NordicPlayground/nrf5-eagle-reference-design/nRF51x22_reference/nRF51x22_qfaa/nRF51x22_qfaa.brd

## EAGLE design nRF51x22_reference/nRF51x22_qfaa/nRF51x22_qfaa.brd (2016-06-28)

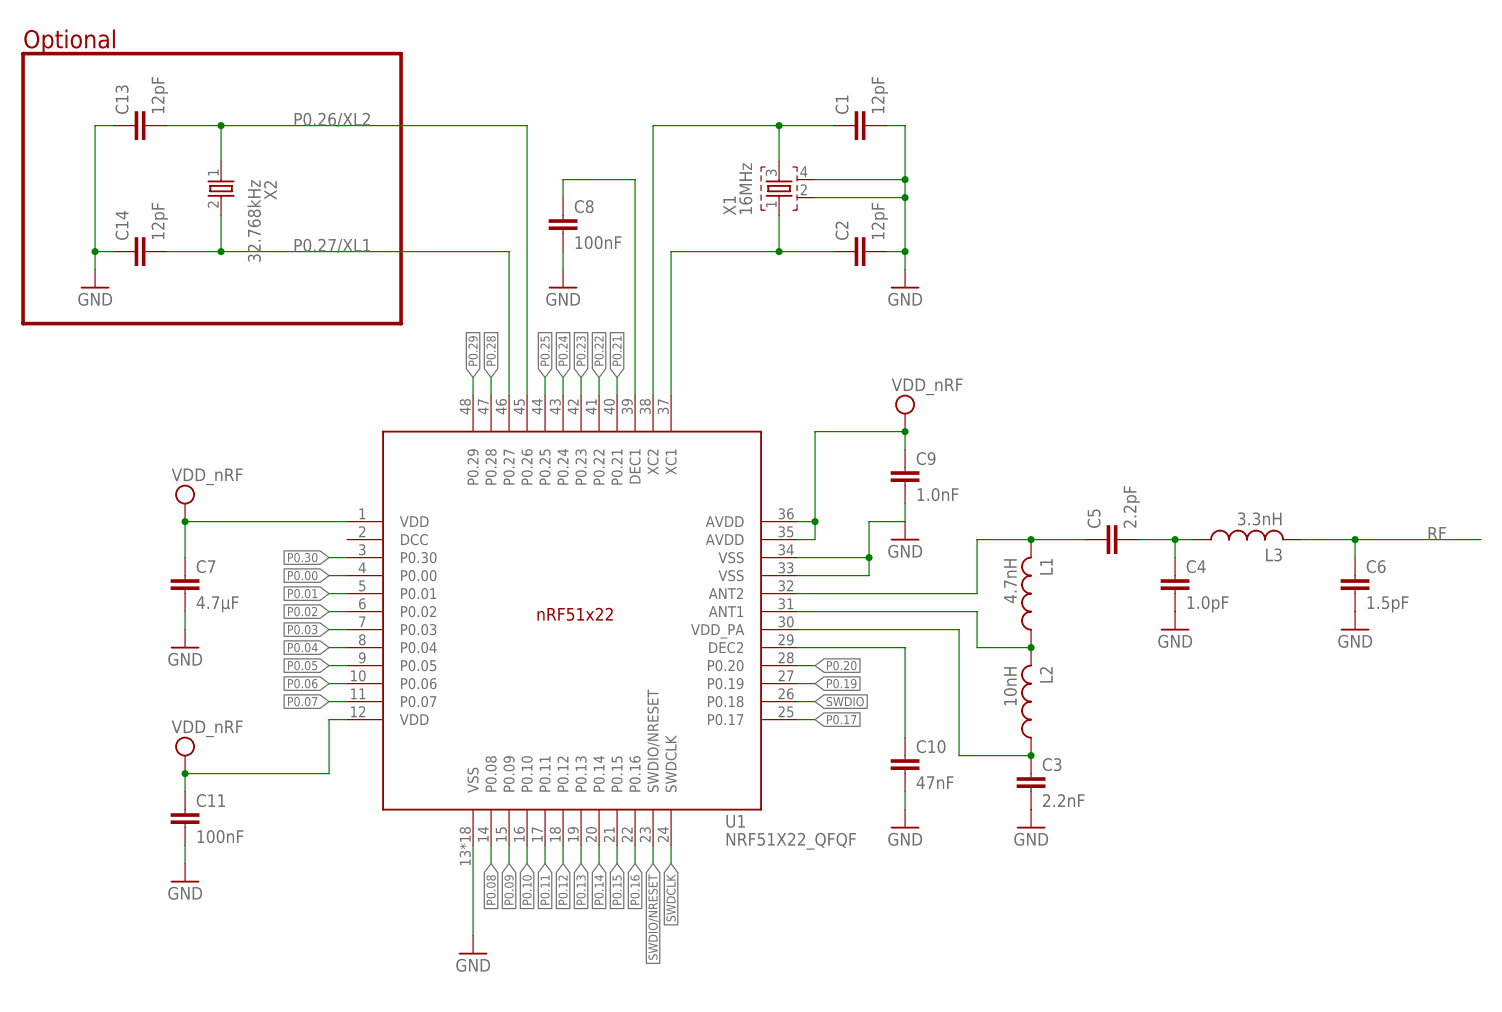
[picture p10: schematic nRF51x22_qfaa.sch]

Parts:
C1, C2, C13, C14: 12pF; RESC0402_N
C3: 2.2nF; RESC0402_N
C4: 1.0pF; RESC0402_N
C5: 2.2pF; RESC0402_N
C6: 1.5pF; RESC0402_N
C7: 4.7µF; RESC0603_N
C8, C11: 100nF; RESC0402_N
C9: 1.0nF; RESC0402_N
C10: 47nF; RESC0402_N
L1: 4.7nH; RESC0402_N
L2: 10nH; RESC0402_N
L3: 3.3nH; RESC0402_N
U1: NRF51X22_QFQF; QFN40P600X600X90-48_N
X1: 16MHz; BT-XTAL_2016_N
X2: 32.768kHz; XTAL_3215_N

Connections:
DCC: U1.2 (DCC)
GND: C1.2, C2.2, C3.2, C4.2, C6.2, C7.2, C8.2, C9.2, C10.2, C11.2, C13.1, C14.1, U1.13 (VSS), U1.33 (VSS), U1.34 (VSS), U1.PAD (VSS), U1.PAD@VIA01 (VSS), U1.PAD@VIA02 (VSS), U1.PAD@VIA03 (VSS), U1.PAD@VIA04 (VSS), U1.PAD@VIA05 (VSS), U1.PAD@VIA06 (VSS), U1.PAD@VIA07 (VSS), U1.PAD@VIA08 (VSS), U1.PAD@VIA09 (VSS), U1.PAD@VIA10 (VSS), U1.PAD@VIA11 (VSS), U1.PAD@VIA12 (VSS), U1.PAD@VIA13 (VSS), U1.PAD@VIA14 (VSS), U1.PAD@VIA15 (VSS), U1.PAD@VIA16 (VSS), X1.2, X1.4
unnamed: L1.1, L2.2, U1.31 (ANT1)
unnamed: C1.1, U1.38 (XC2), X1.3
unnamed: C10.1, U1.29 (DEC2)
unnamed: C8.1, U1.39 (DEC1)
unnamed: C3.1, L2.1, U1.30 (VDD_PA)
unnamed: C5.1, L1.2, U1.32 (ANT2)
unnamed: C4.1, C5.2, L3.1
P0.00: U1.4 (P0.00)
P0.01: U1.5 (P0.01)
P0.02: U1.6 (P0.02)
P0.03: U1.7 (P0.03)
P0.04: U1.8 (P0.04)
P0.05: U1.9 (P0.05)
P0.06: U1.10 (P0.06)
P0.07: U1.11 (P0.07)
P0.08: U1.14 (P0.08)
P0.09: U1.15 (P0.09)
P0.10: U1.16 (P0.10)
P0.11: U1.17 (P0.11)
P0.12: U1.18 (P0.12)
P0.13: U1.19 (P0.13)
P0.14: U1.20 (P0.14)
P0.15: U1.21 (P0.15)
P0.16: U1.22 (P0.16)
P0.17: U1.25 (P0.17)
P0.19: U1.27 (P0.19)
P0.20: U1.28 (P0.20)
P0.21: U1.40 (P0.21)
P0.22: U1.41 (P0.22)
P0.23: U1.42 (P0.23)
P0.24: U1.43 (P0.24)
P0.25: U1.44 (P0.25)
P0.26/XL2: C13.2, U1.45 (P0.26), X2.1
P0.27/XL1: C14.2, U1.46 (P0.27), X2.2
P0.28: U1.47 (P0.28)
P0.29: U1.48 (P0.29)
P0.30: U1.3 (P0.30)
RF: C6.1, L3.2
SWDCLK: U1.24 (SWDCLK)
SWDIO: U1.26 (P0.18)
SWDIO/NRESET: U1.23 (SWDIO/NRESET)
VDD_NRF: C7.1, C9.1, C11.1, U1.1 (VDD), U1.12 (VDD), U1.35 (AVDD), U1.36 (AVDD)
X1: C2.1, U1.37 (XC1), X1.1

Notes on the sheet:
Optional

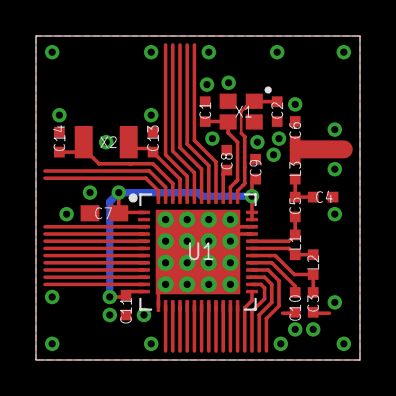
[picture p11: board nRF51x22_qfaa.brd from above]

Board: 2 copper layers, 18.0 x 18.0 mm, 19 parts (0 on the bottom side), 13 nets.
