NordicPlayground/nrf5-eagle-reference-design/nRF52832_MCU_Board/nRF52832_MCU_nano/nRF52832_MCU.brd

## EAGLE design nRF52832_MCU_Board/nRF52832_MCU_nano/nRF52832_MCU.brd (2016-06-23)

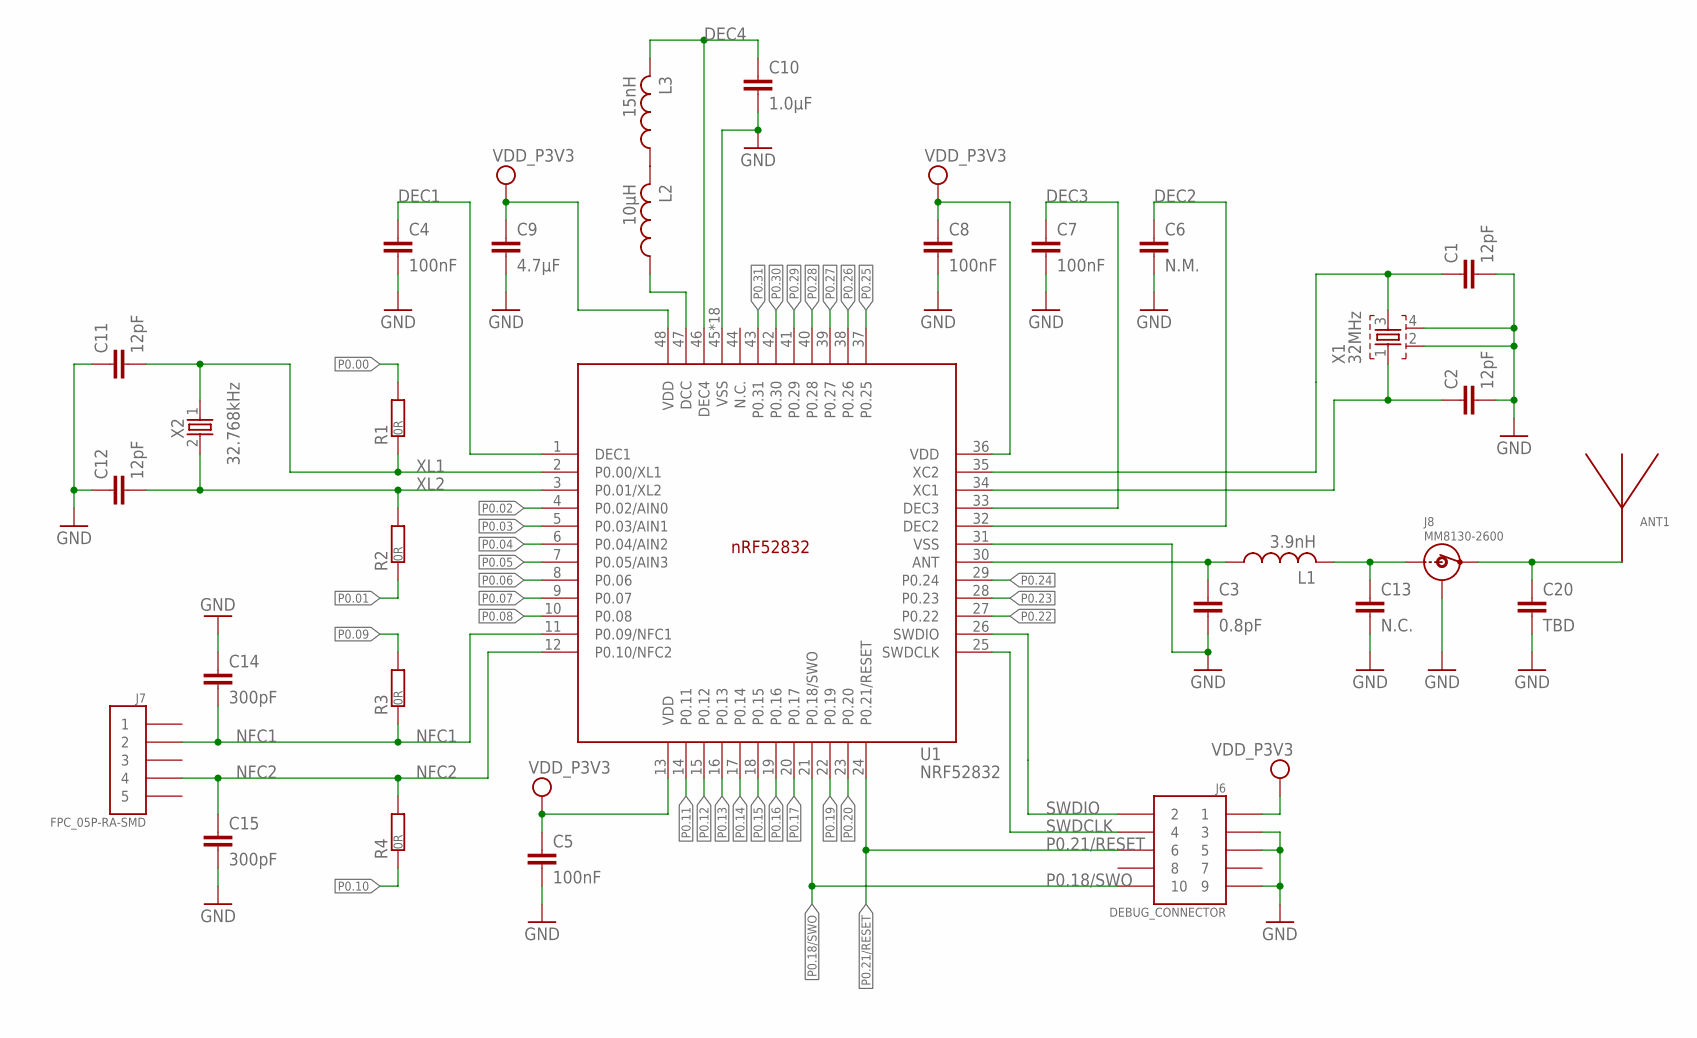
[picture p12: schematic nRF52832_MCU.sch, sheet 1]

Parts:
ANT1: ANTENNA_QUARTER-WAVE_MONOPOLE_MEANDERED_LEFT; QWMP_MEANDERED_LEFT_+6
C1, C2, C11, C12: 12pF; RESC0402_N
C3: 0.8pF; RESC0402_N
C4, C5, C7, C8: 100nF; RESC0402_N
C6: N.M.; RESC0402_N
C9: 4.7µF; RESC0603_N
C10: 1.0µF; RESC0603_N
C13: N.C.; RESC0402_N
C14, C15: 300pF; RESC0402_N
C20: TBD; RESC0402_N
J6: DEBUG_CONNECTOR; HDRV127P5X2-10_N
J7: FPC_05P-RA-SMD
J8: MM8130-2600
L1: 3.9nH; RESC0402_N
L2: 10µH; RESC0603_N
L3: 15nH; RESC0402_N
R1, R2, R3, R4: 0R; RESC0402_N
U1: NRF52832; QFN40P600X600X90-48_N
X1: 32MHz; BT-XTAL_2016_N
X2: 32.768kHz; XTAL_3215_N

Connections:
ANT: C3.1, L1.1, U1.30 (ANT)
DEC1: C4.1, U1.1 (DEC1)
DEC2: C6.1, U1.32 (DEC2)
DEC3: C7.1, U1.33 (DEC3)
DEC4: C10.1, L3.2, U1.46 (DEC4)
GND: C1.2, C2.2, C3.2, C4.2, C5.2, C6.2, C7.2, C8.2, C9.2, C10.2, C11.1, C12.1, C13.2, C14.1, C15.2, C20.2, J6.3, J6.5, J6.9, J8.1, J8.2, J8.3, J8.4, U1.31 (VSS), U1.45 (VSS), U1.PAD (VSS), U1.PAD@VIA01 (VSS), U1.PAD@VIA02 (VSS), U1.PAD@VIA03 (VSS), U1.PAD@VIA04 (VSS), U1.PAD@VIA05 (VSS), U1.PAD@VIA06 (VSS), U1.PAD@VIA07 (VSS), U1.PAD@VIA08 (VSS), U1.PAD@VIA09 (VSS), U1.PAD@VIA10 (VSS), U1.PAD@VIA11 (VSS), U1.PAD@VIA12 (VSS), U1.PAD@VIA13 (VSS), U1.PAD@VIA14 (VSS), U1.PAD@VIA15 (VSS), U1.PAD@VIA16 (VSS), X1.2, X1.4; also elsewhere on the board
unnamed: ANT1.P$1, C20.1, J8.OUT
unnamed: L2.2, L3.1
unnamed: C1.1, U1.35 (XC2), X1.3
unnamed: L2.1, U1.47 (DCC)
unnamed: C13.1, J8.IN, L1.2
NFC1: C14.2, J7.2, R3.1, U1.11 (P0.09/NFC1)
NFC2: C15.1, J7.4, R4.2, U1.12 (P0.10/NFC2)
P0.00: R1.2; also elsewhere on the board
P0.01: R2.1; also elsewhere on the board
P0.02: U1.4 (P0.02/AIN0); also elsewhere on the board
P0.03: U1.5 (P0.03/AIN1); also elsewhere on the board
P0.04: U1.6 (P0.04/AIN2); also elsewhere on the board
P0.05: U1.7 (P0.05/AIN3); also elsewhere on the board
P0.06: U1.8 (P0.06); also elsewhere on the board
P0.07: U1.9 (P0.07); also elsewhere on the board
P0.08: U1.10 (P0.08); also elsewhere on the board
P0.09: R3.2; also elsewhere on the board
P0.10: R4.1; also elsewhere on the board
P0.11: U1.14 (P0.11); also elsewhere on the board
P0.12: U1.15 (P0.12); also elsewhere on the board
P0.13: U1.16 (P0.13); also elsewhere on the board
P0.14: U1.17 (P0.14); also elsewhere on the board
P0.15: U1.18 (P0.15); also elsewhere on the board
P0.16: U1.19 (P0.16); also elsewhere on the board
P0.17: U1.20 (P0.17); also elsewhere on the board
P0.18/SWO: J6.10, U1.21 (P0.18/SWO); also elsewhere on the board
P0.19: U1.22 (P0.19); also elsewhere on the board
P0.20: U1.23 (P0.20); also elsewhere on the board
P0.21/RESET: J6.6, U1.24 (P0.21/RESET); also elsewhere on the board
P0.22: U1.27 (P0.22); also elsewhere on the board
P0.23: U1.28 (P0.23); also elsewhere on the board
P0.24: U1.29 (P0.24); also elsewhere on the board
P0.25: U1.37 (P0.25); also elsewhere on the board
P0.26: U1.38 (P0.26); also elsewhere on the board
P0.27: U1.39 (P0.27); also elsewhere on the board
P0.28: U1.40 (P0.28); also elsewhere on the board
P0.29: U1.41 (P0.29); also elsewhere on the board
P0.30: U1.42 (P0.30); also elsewhere on the board
P0.31: U1.43 (P0.31); also elsewhere on the board
SWDCLK: J6.4, U1.25 (SWDCLK)
SWDIO: J6.2, U1.26 (SWDIO)
VDD_P3V3: C5.1, C8.1, C9.1, J6.1, U1.13 (VDD), U1.36 (VDD), U1.48 (VDD); also elsewhere on the board
X1: C2.1, U1.34 (XC1), X1.1
XL1: C11.2, R1.1, U1.2 (P0.00/XL1), X2.1
XL2: C12.2, R2.2, U1.3 (P0.01/XL2), X2.2

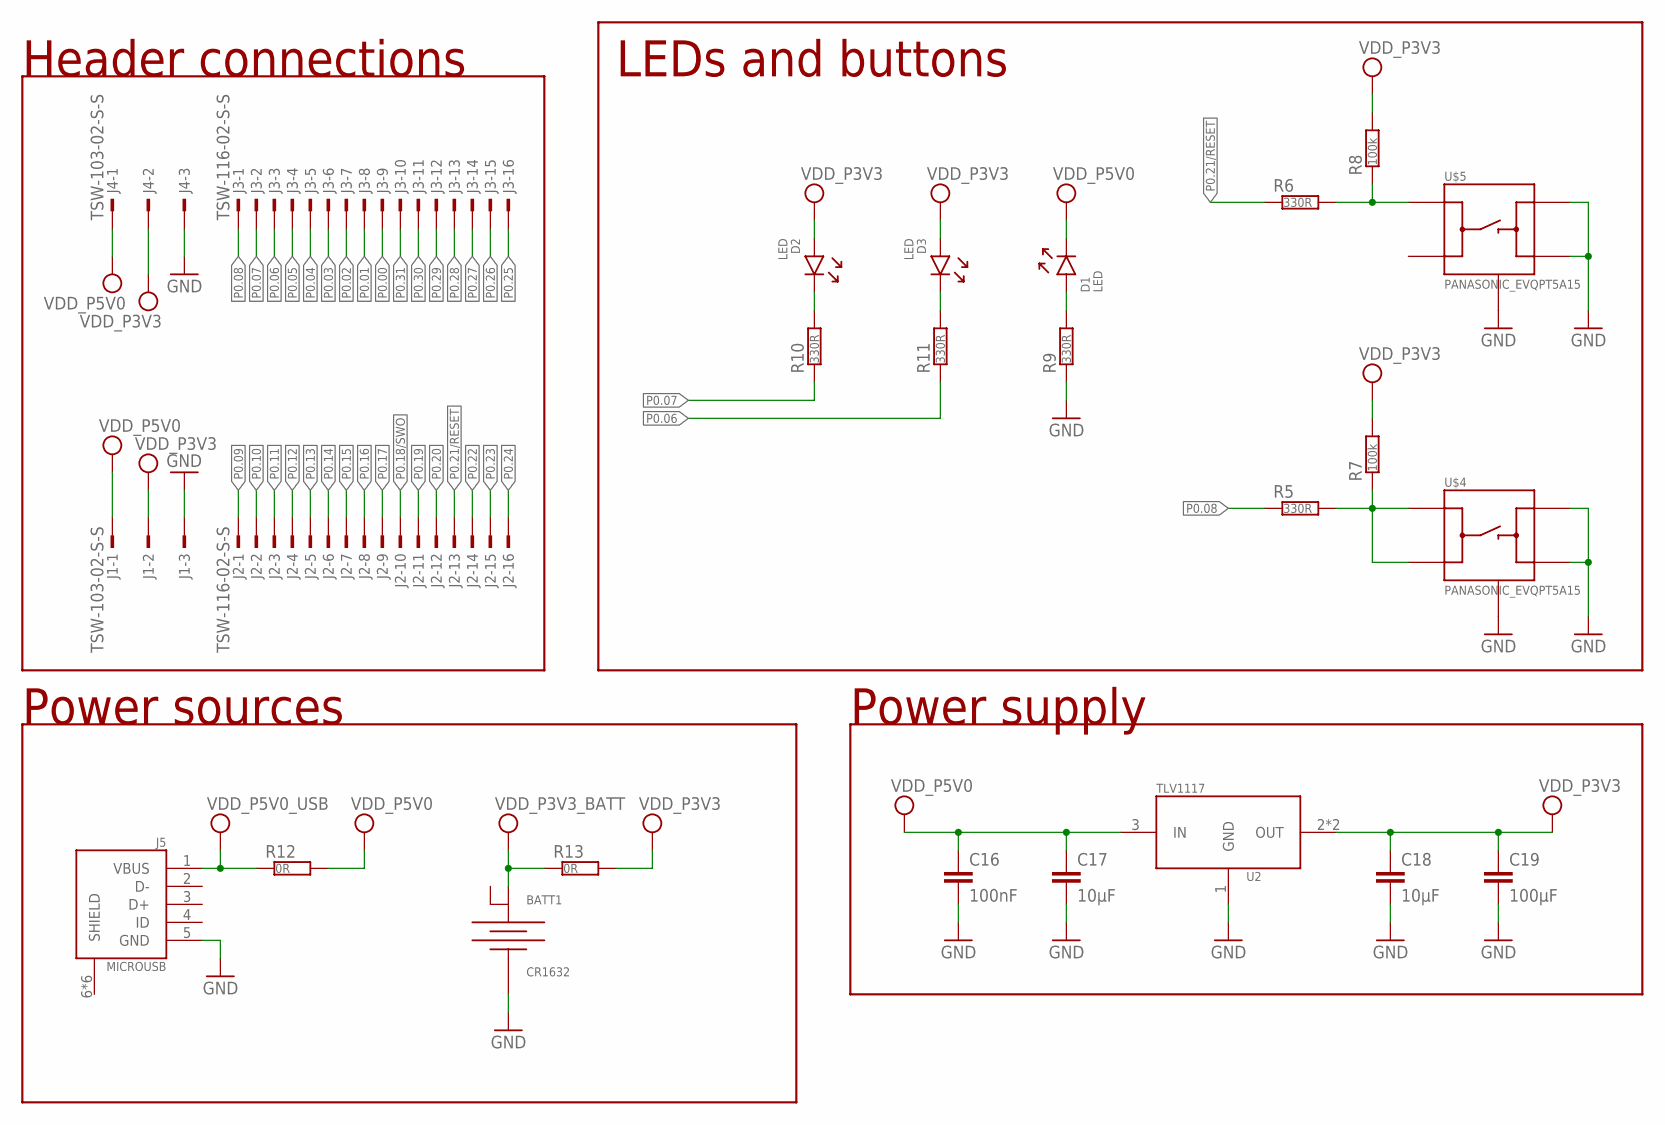
[picture p13: schematic nRF52832_MCU.sch, sheet 2]

Parts:
BATT1: CR1632; CR1632_HOLDER_TH
C16: 100nF; RESC0402_N
C17, C18: 10µF; RESC0603_N
C19: 100µF; RESC0805_N
D1, D2, D3: LED; DIOC0603_N
J1, J4: TSW-103-02-S-S
J2, J3: TSW-116-02-S-S
J5: MICROUSB; USB-MICRO-B-RA-SMD-PIP
R5, R6, R9, R10, R11: 330R; RESC0402_N
R7, R8: 100k; RESC0402_N
R12, R13: 0R; RESC0402_N
U2: TLV1117; SOT220P700-4_N
U$4, U$5: PANASONIC_EVQPT5A15

Connections:
GND: BATT1.1 (-), C16.2, C17.2, C18.2, C19.2, J1.3, J4.3, J5.5 (GND), R9.1, U2.1 (GND), U$4.3 (B), U$4.4 (B'), U$4.5 (GND), U$4.6 (GND), U$5.3 (B), U$5.4 (B'), U$5.5 (GND), U$5.6 (GND); also elsewhere on the board
unnamed: R6.2, R8.1, U$5.1 (A)
unnamed: R5.2, R7.1, U$4.1 (A), U$4.2 (A')
unnamed: D2.1 (C), R10.2
unnamed: D3.1 (C), R11.2
P0.00: J3.9; also elsewhere on the board
P0.01: J3.8; also elsewhere on the board
P0.02: J3.7; also elsewhere on the board
P0.03: J3.6; also elsewhere on the board
P0.04: J3.5; also elsewhere on the board
P0.05: J3.4; also elsewhere on the board
P0.06: J3.3, R11.1; also elsewhere on the board
P0.07: J3.2, R10.1; also elsewhere on the board
P0.08: J3.1, R5.1; also elsewhere on the board
P0.09: J2.1; also elsewhere on the board
P0.10: J2.2; also elsewhere on the board
P0.11: J2.3; also elsewhere on the board
P0.12: J2.4; also elsewhere on the board
P0.13: J2.5; also elsewhere on the board
P0.14: J2.6; also elsewhere on the board
P0.15: J2.7; also elsewhere on the board
P0.16: J2.8; also elsewhere on the board
P0.17: J2.9; also elsewhere on the board
P0.18/SWO: J2.10; also elsewhere on the board
P0.19: J2.11; also elsewhere on the board
P0.20: J2.12; also elsewhere on the board
P0.21/RESET: J2.13, R6.1; also elsewhere on the board
P0.22: J2.14; also elsewhere on the board
P0.23: J2.15; also elsewhere on the board
P0.24: J2.16; also elsewhere on the board
P0.25: J3.16; also elsewhere on the board
P0.26: J3.15; also elsewhere on the board
P0.27: J3.14; also elsewhere on the board
P0.28: J3.13; also elsewhere on the board
P0.29: J3.12; also elsewhere on the board
P0.30: J3.11; also elsewhere on the board
P0.31: J3.10; also elsewhere on the board
VCC_P5V0_USB: J5.1 (VBUS), R12.1
VDD_LED: D1.2 (A), R9.2
VDD_P3V3: C18.1, C19.1, D2.2 (A), D3.2 (A), J1.2, J4.2, R7.2, R8.2, R13.2, U2.2 (OUT), U2.4 (OUT); also elsewhere on the board
VDD_P3V3_BATT: BATT1.2 (+), R13.1
VDD_P5V0: C16.1, C17.1, D1.1 (C), J1.1, J4.1, R12.2, U2.3 (IN)

Notes on the sheet:
Power supply
Power sources
Header connections
LEDs and buttons
