NordicPlayground/nrf5-eagle-reference-design/nRF52832_MCU_Board/nRF52832_MCU_nano/nRF52832_MCU.brd

## EAGLE design nRF52832_MCU_Board/nRF52832_MCU_nano/nRF52832_MCU.brd (continued)

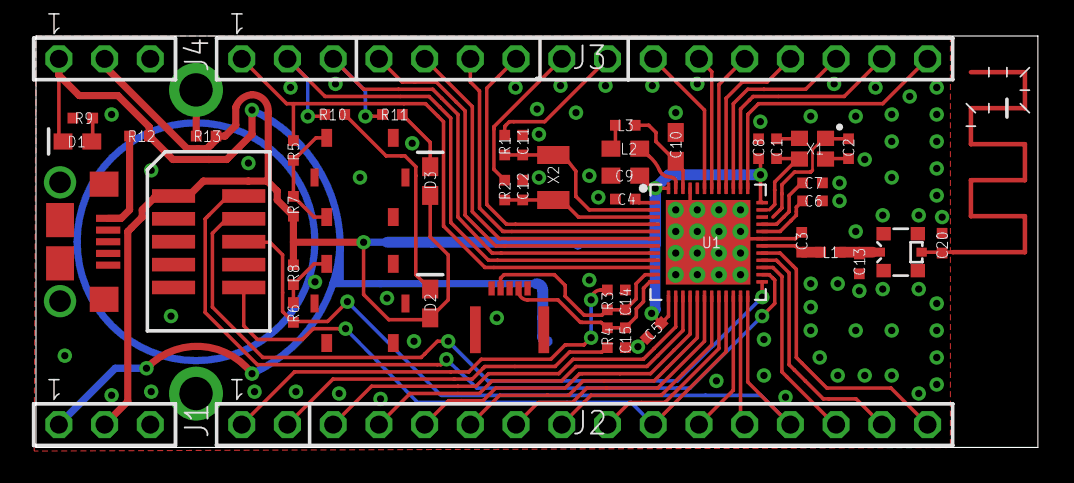
[picture p14: board nRF52832_MCU.brd from above]

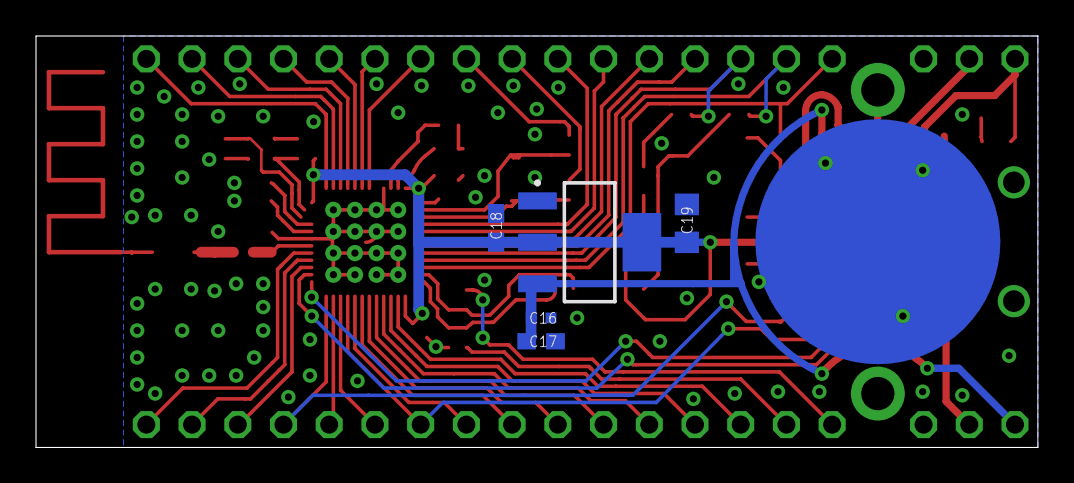
[picture p15: board nRF52832_MCU.brd from below]

Board: 2 copper layers, 55.7 x 22.9 mm, 55 parts (6 on the bottom side), 59 nets.
